johnmknight/Console10/stl/nasa switch  guards/108963-space-shuttle-toggle-switch-guard-1ca99f90-c89b-49a0-a293-3f26a061288c.pdf

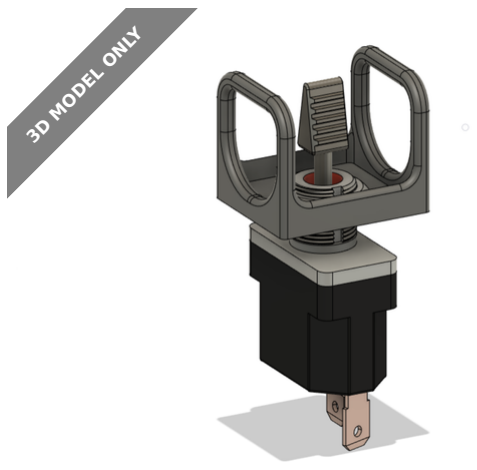
[picture p2: figure]
3D MODEL ONLY

## Summary

An accurate model of a standard space shuttle toggle switch guard, with

switch head.

Hobby & Makers (https://www.printables.com/model?categoryId=48) | > | Mechanical Parts (https://www.printables.com/model?categoryId=51)
Tags: spacex | space | rocket | switch | engineering | controller
spaceship | scifi | nasa | resin | resinprinter | toggleswitch
toggle | controlpanel | shuttle | spaceshuttle

This is an accurate recreation of a toggle switch guard used on the many

control panels in the space shuttle.

Included is a PDF are the part dimensions in case the standard thread

dimensions of the switch are different from what you choose to you use for

your project, and want to remodel it. I have also included two variations of

the switch head, one with hole and one without.

I recommend using a resin printer for the best results, and for added

realism making a cold cast copy for realistic metal weight and texture.

I have yet to find a good model of toggle switch that can be modified so

that the head can be put on, and not rotate in place without heavy switch

modification or damage. If anyone can find one please share!

I (https://www.printables.com/social/198340/about) ImAThingsGuy (https://www.printables.com/social/198340/about)

## Space Shuttle

## Toggle Switch

## Guard

VIEW IN BROWSER (https://www.printables.com/model/108963-space-shuttle-toggle-switch-guard)

updated 30. 12. 2021 | published 30. 12. 2021

## Model files

## Other files

Also please share any remixes of this or any projects you use this design

on. I have wanted to make a space shuttle/apollo cockpit styled control

panel for many years now but have never gotten around to it, I would love

to see anyone else's attempt at it or something similar.

Fun Fact; The real toggle switch guards were made of titanium to prevent

sparks in the capsule, among other reasons I'm sure.

## License

This work is licensed under a

Creative Commons (International License)

Public Domain (https://creativecommons.org/share-your-work/public-domain/cc0/)

space-shuttle-switch-head-with-hole.stl

space-shuttle-switch-head.stl

space-shuttle-switch-guard.stl

suttle-switch-final-drawing-v1.pdf

✔ | Sharing without ATTRIBUTION
✔ | Remix Culture allowed
✔ | Commercial Use
✔ | Free Cultural Works
✔ | Meets Open Definition
