johnmknight/Console10/branding/console10_social_preview.png

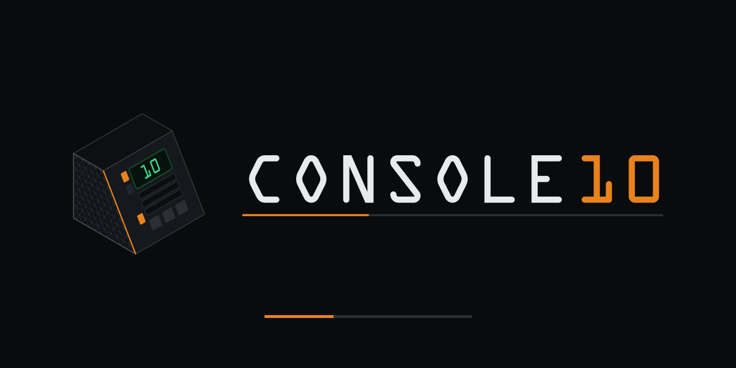
branding/console10_social_preview.png
