johnmknight/Console10/marketing/overlays/overlay_4u_front.png

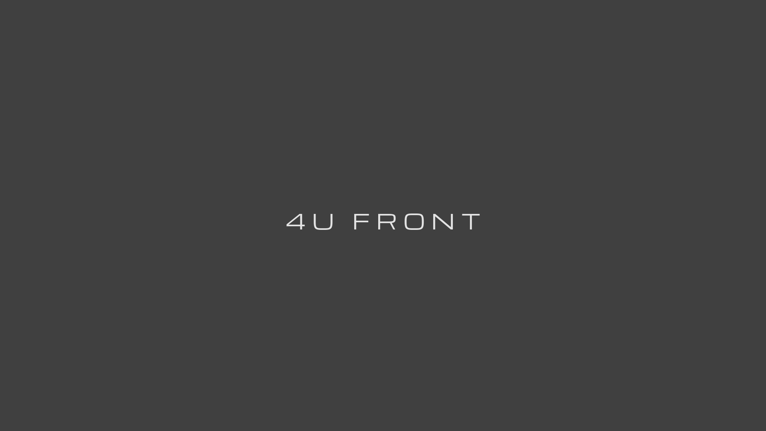
marketing/overlays/overlay_4u_front.png
