johnmknight/Console10/marketing/overlays/overlay_endcard.png

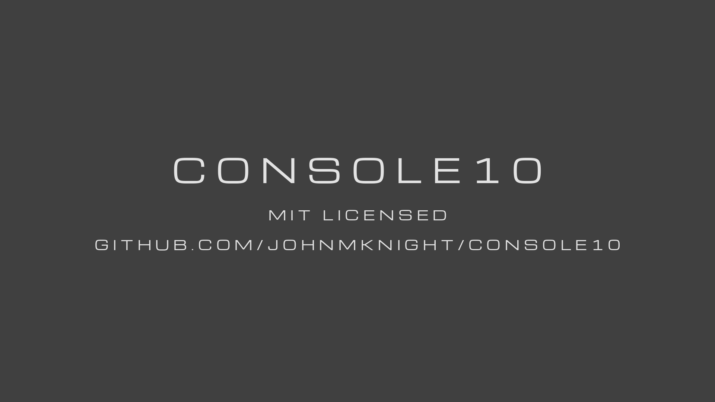
marketing/overlays/overlay_endcard.png
