johnmknight/Console10/marketing/overlays/overlay_partcount.png

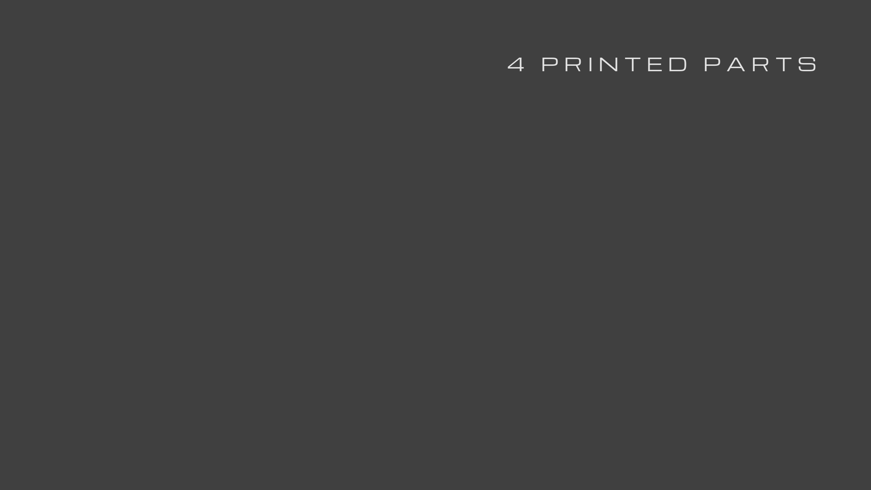
marketing/overlays/overlay_partcount.png
