johnmknight/Console10/preview/asm_macropad_iso.png

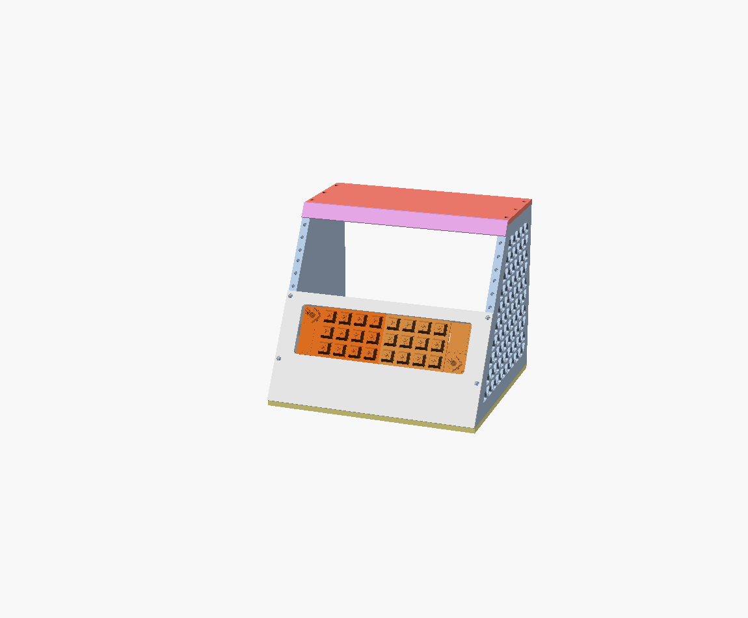
preview/asm_macropad_iso.png
