johnmknight/Console10/preview/asm_macropad_side.png

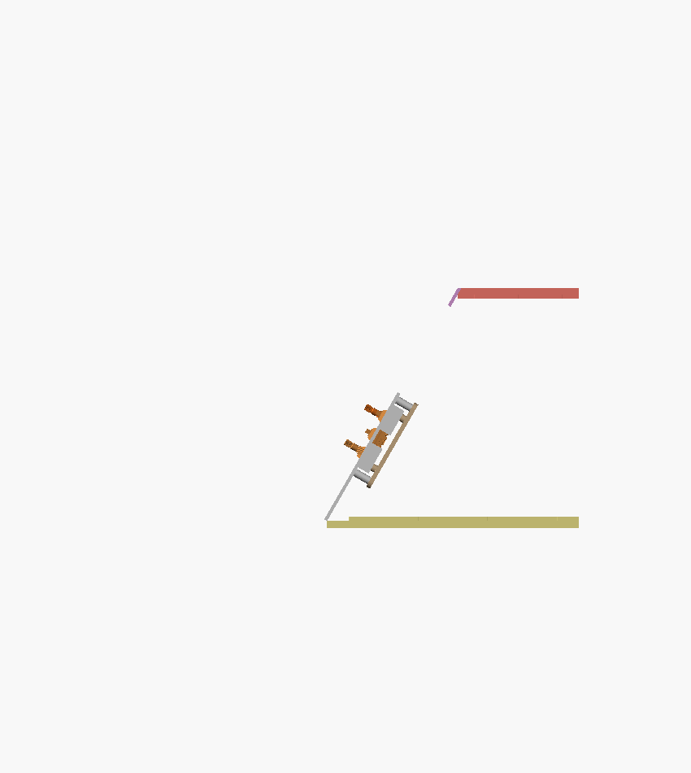
preview/asm_macropad_side.png
