johnmknight/Console10/preview/cheek_perimeter_iso.png

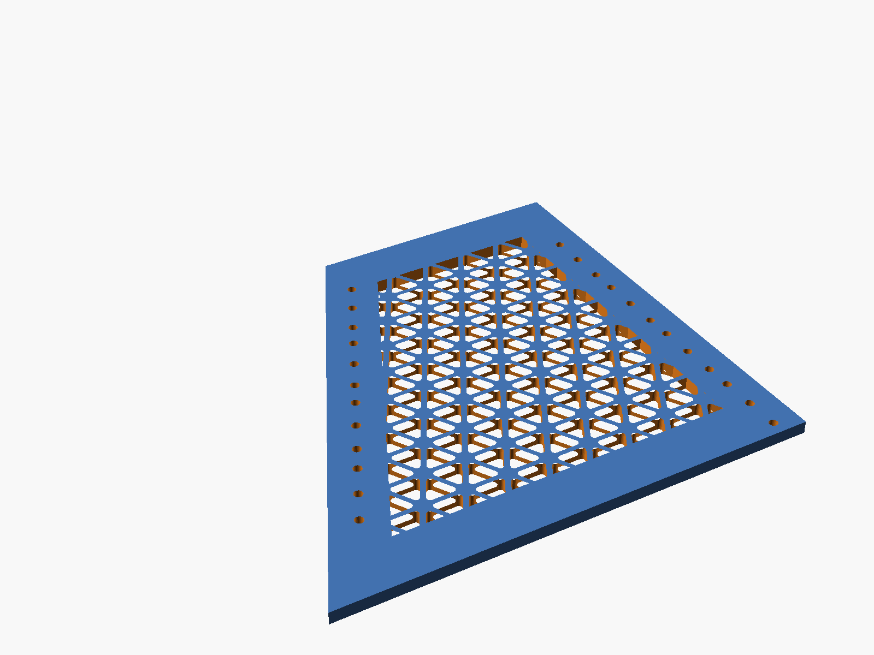
preview/cheek_perimeter_iso.png
