johnmknight/Console10/preview/cheek_perimeter_top.png

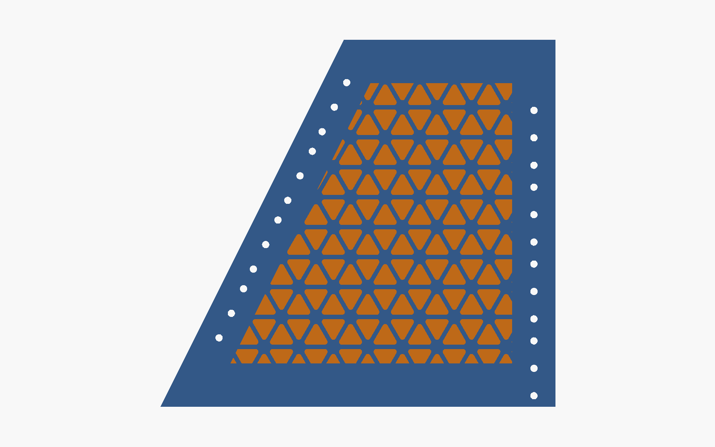
preview/cheek_perimeter_top.png
