johnmknight/Console10/preview/dsky_front.png

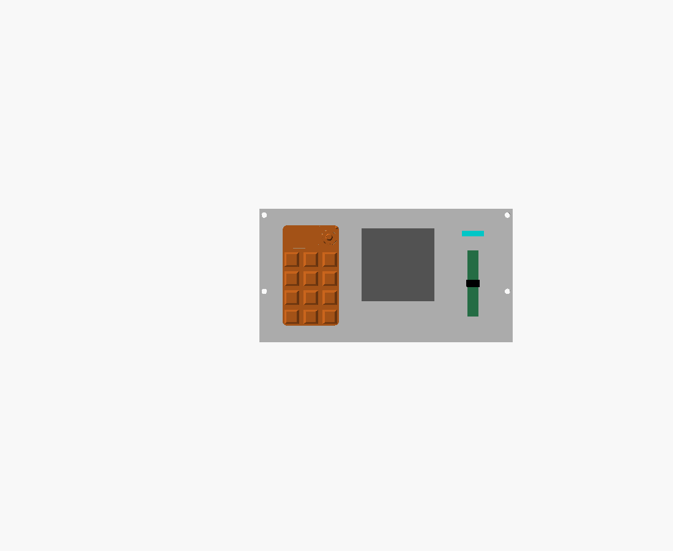
preview/dsky_front.png
