johnmknight/Console10/preview/dsky_iso.png

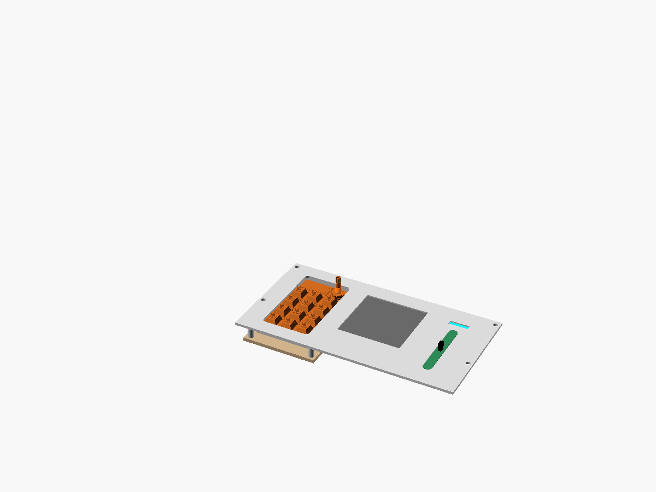
preview/dsky_iso.png
