johnmknight/Console10/preview/dsky_rear.png

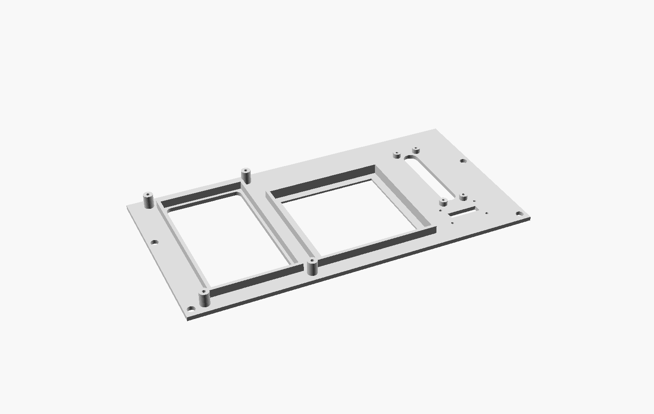
preview/dsky_rear.png
