johnmknight/Console10/preview/guard_A_front.png

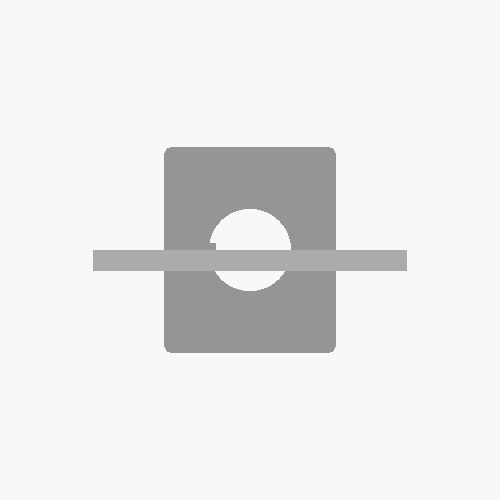
preview/guard_A_front.png
