johnmknight/Console10/preview/guard_A_top.png

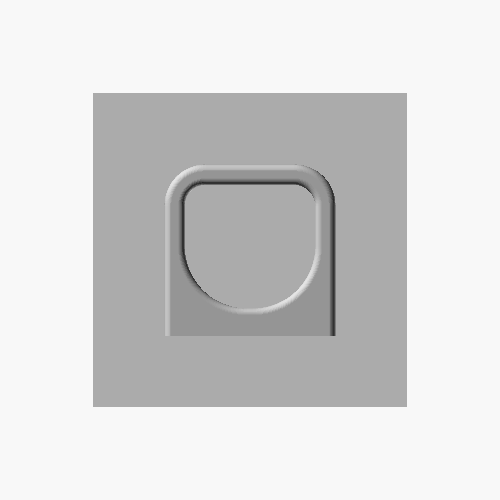
preview/guard_A_top.png
