johnmknight/Console10/preview/guard_front.png

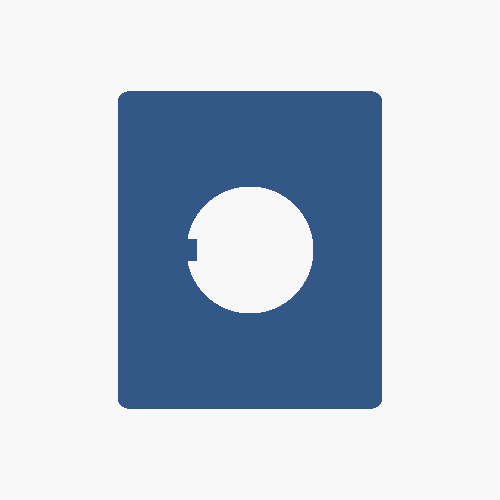
preview/guard_front.png
