johnmknight/Console10/preview/guard_side.png

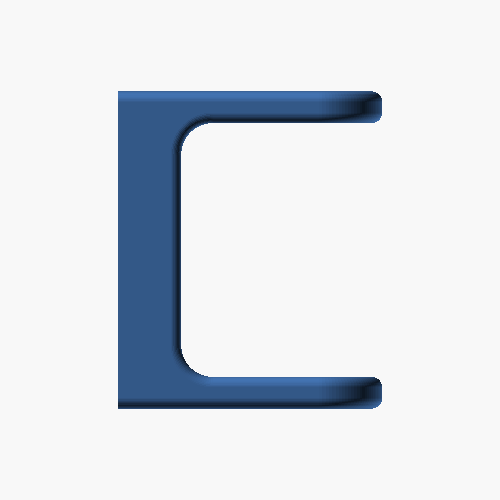
preview/guard_side.png
