johnmknight/Console10/preview/guard_stand_A.png

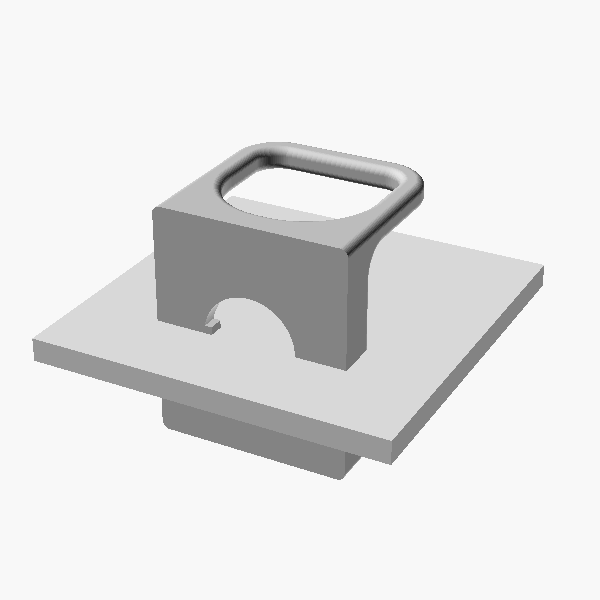
preview/guard_stand_A.png
