johnmknight/Console10/preview/guard_top.png

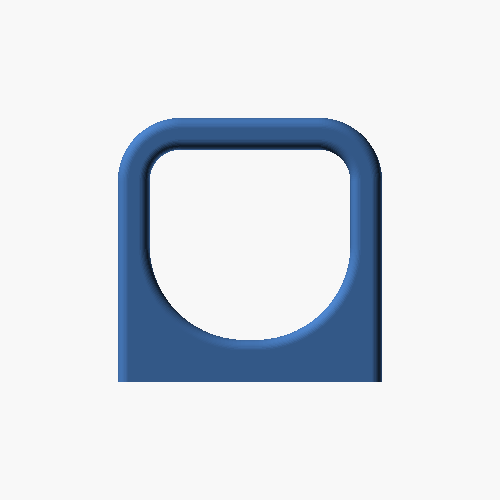
preview/guard_top.png
