johnmknight/Console10/preview/hp_backplate.png

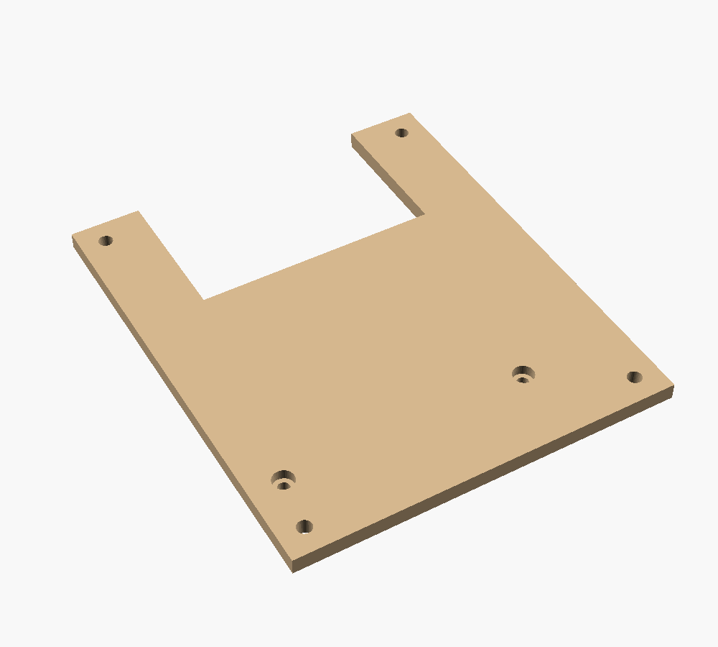
preview/hp_backplate.png
