johnmknight/Console10/preview/hp_sq_front.png

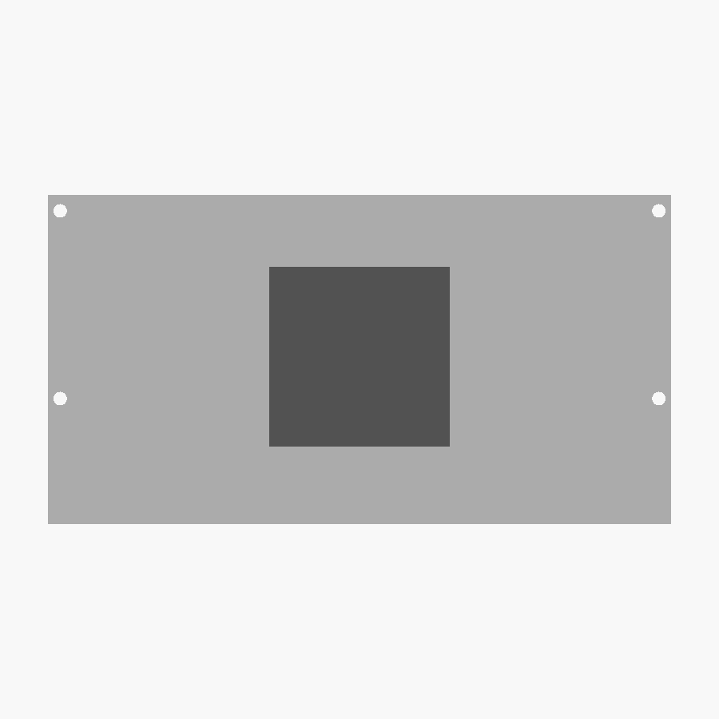
preview/hp_sq_front.png
