johnmknight/Console10/preview/hp_sq_iso.png

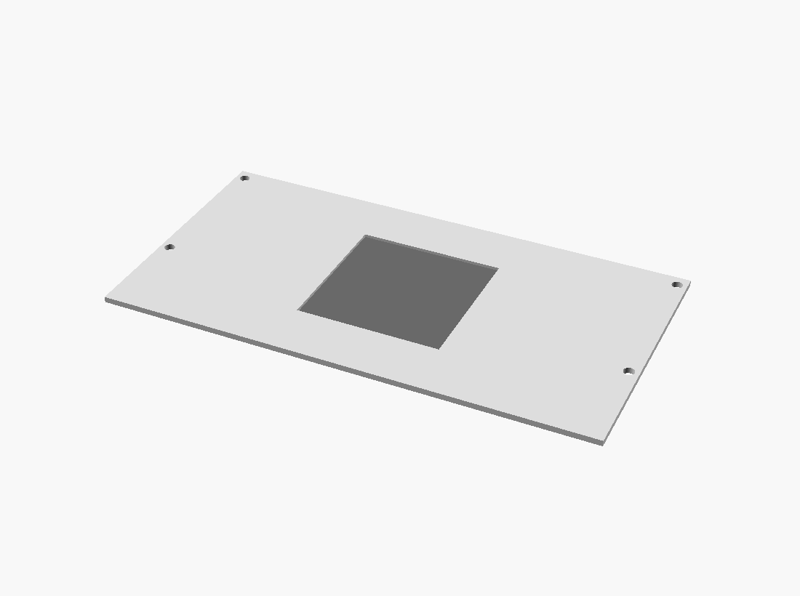
preview/hp_sq_iso.png
