johnmknight/Console10/preview/mp_pair_front.png

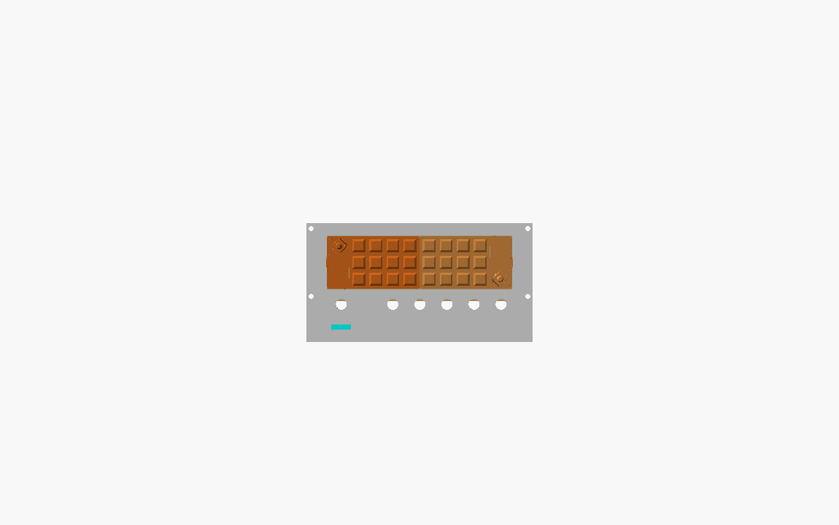
preview/mp_pair_front.png
