johnmknight/Console10/preview/oled_closeup.png

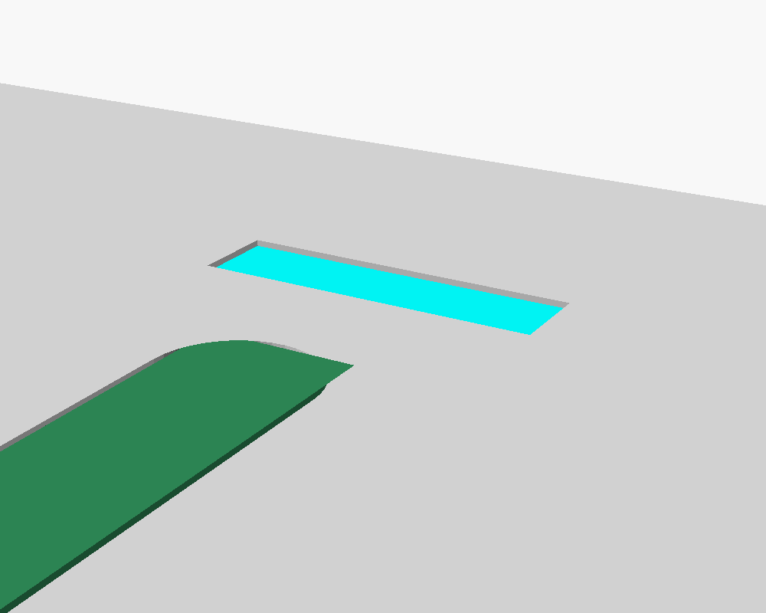
preview/oled_closeup.png
