johnmknight/Console10/preview/ref_bracket_top.png

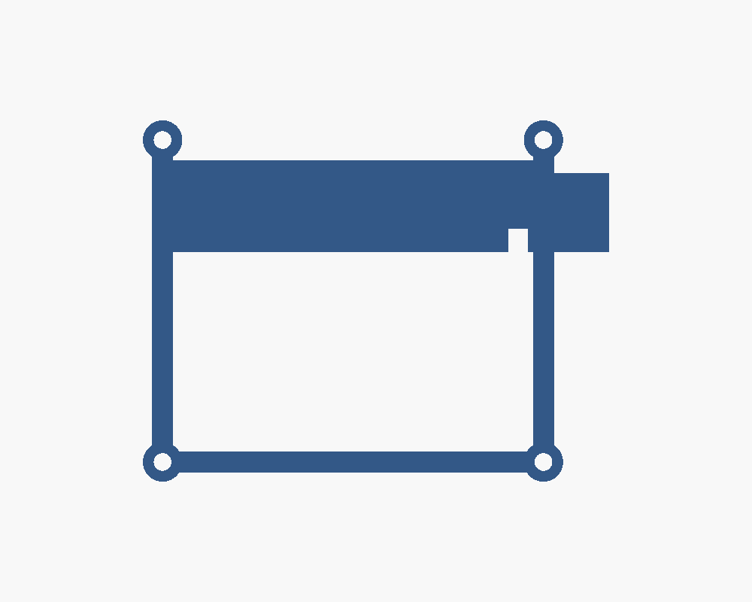
preview/ref_bracket_top.png
