johnmknight/Console10/preview/ref_wallback_bot.png

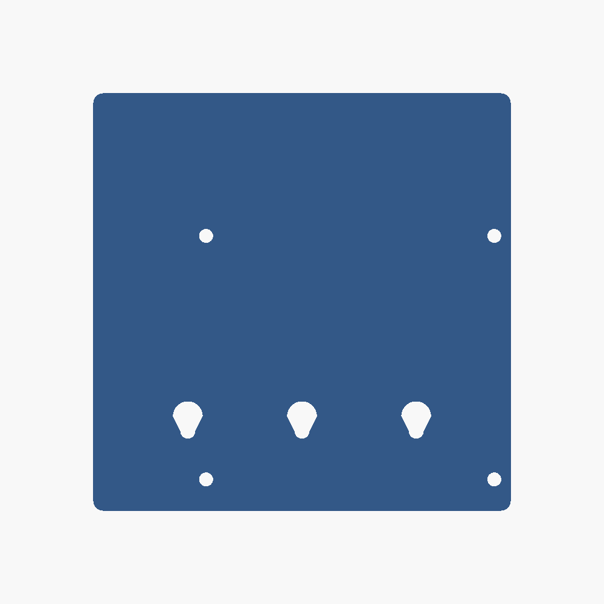
preview/ref_wallback_bot.png
