johnmknight/Console10/preview/ref_wallback_iso.png

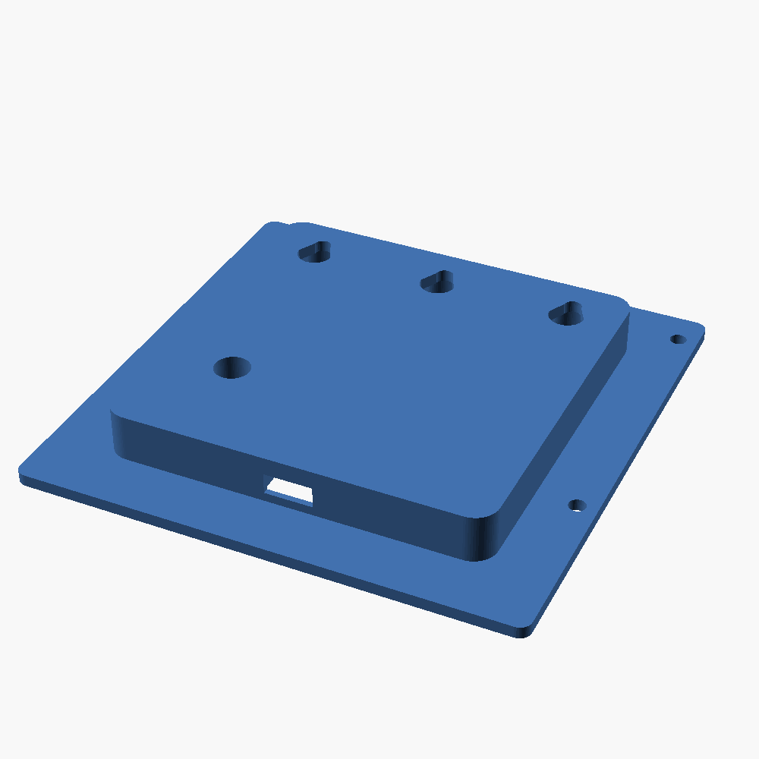
preview/ref_wallback_iso.png
