johnmknight/Console10/preview/ref_wallback_top.png

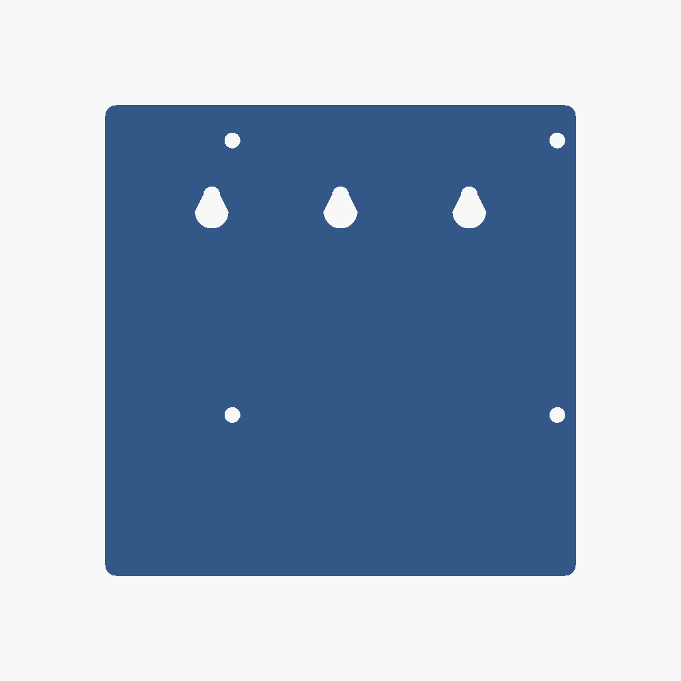
preview/ref_wallback_top.png
