johnmknight/Console10/preview/screen_slider_front.png

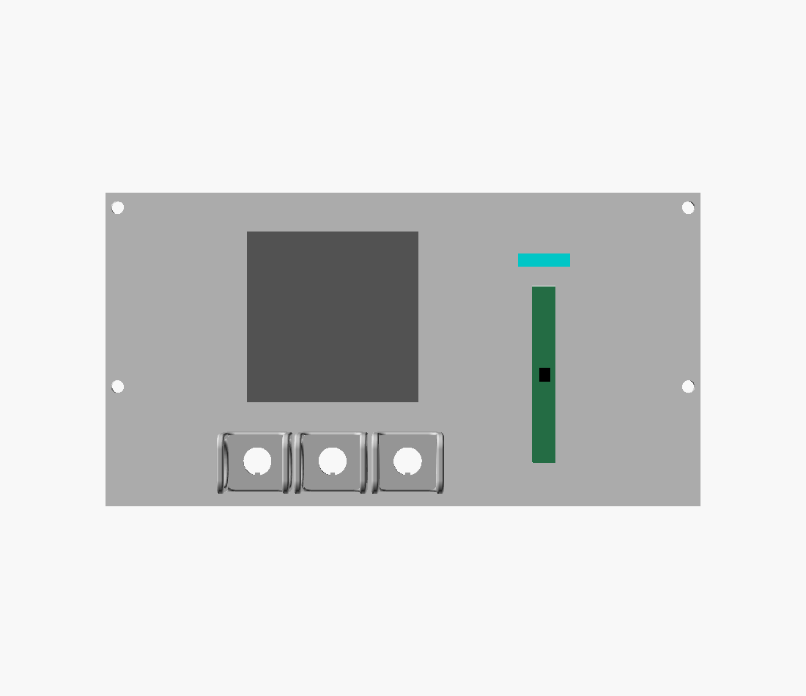
preview/screen_slider_front.png
