johnmknight/Console10/preview/screen_slider_iso.png

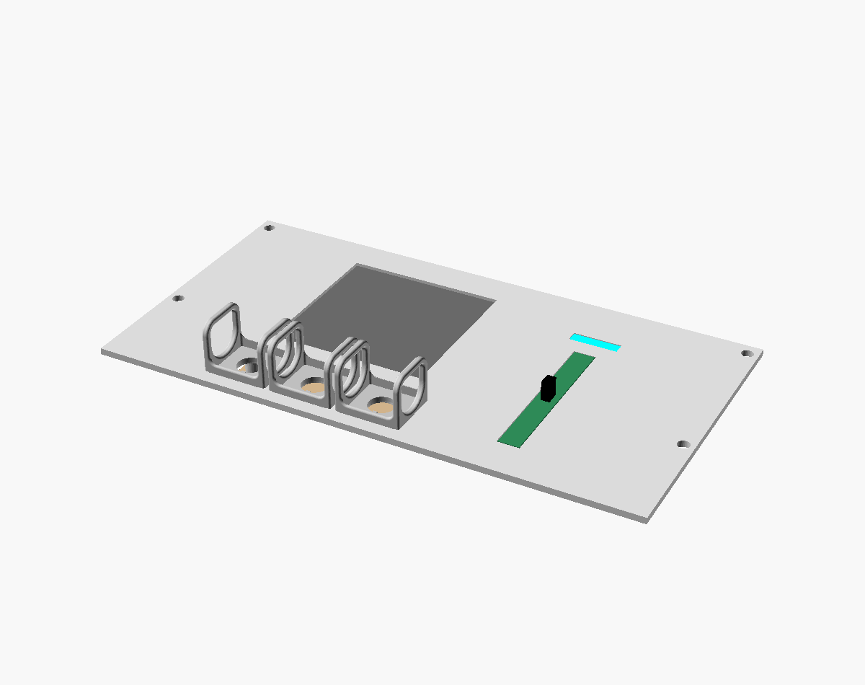
preview/screen_slider_iso.png
