johnmknight/Console10/preview/screen_slider_rear.png

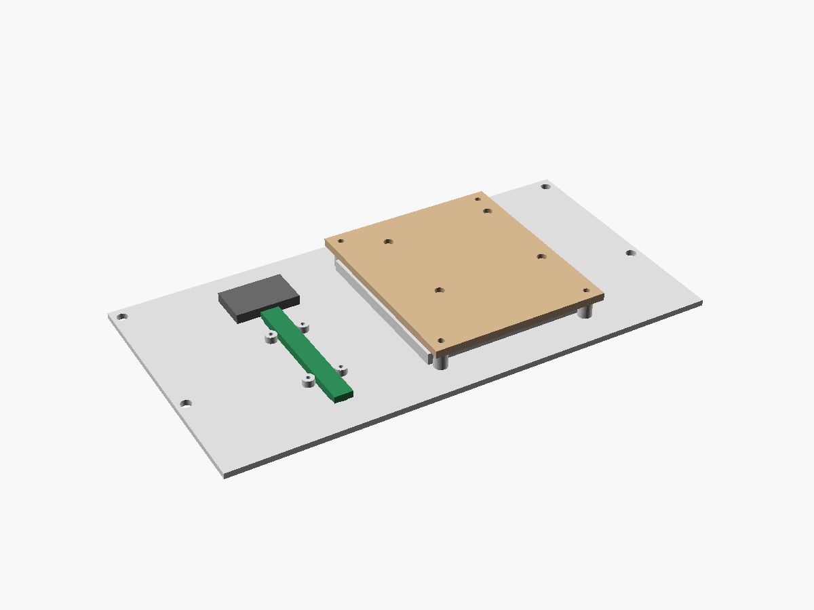
preview/screen_slider_rear.png
