johnmknight/Console10/preview/screen_slider_sec.png

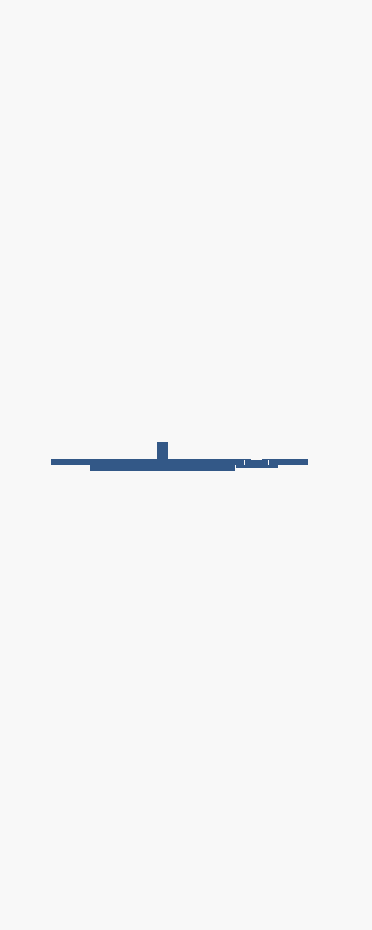
preview/screen_slider_sec.png
