johnmknight/Console10/preview/slider_closeup.png

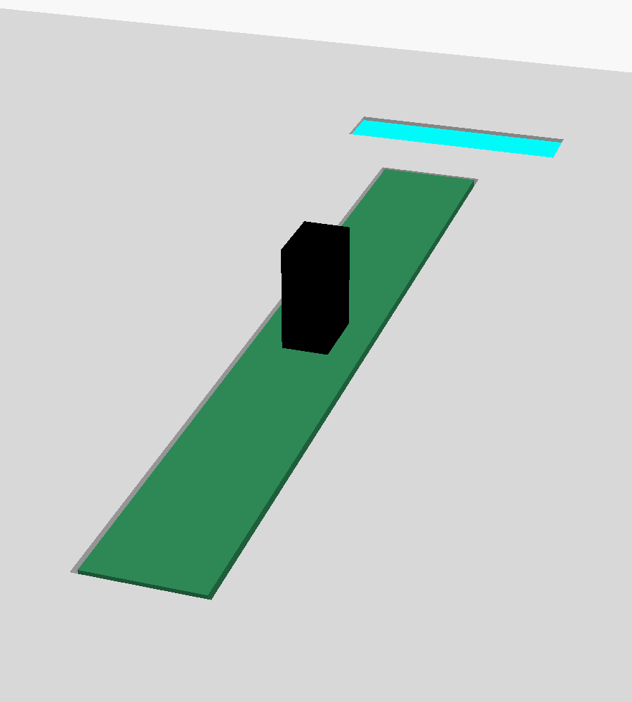
preview/slider_closeup.png
