johnmknight/Console10/stl/Console10_phone_2u_lever.stl

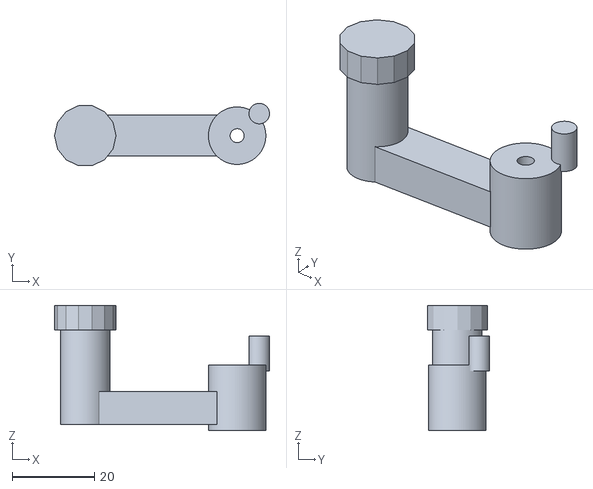
[picture p51: CAD file, 2026-08-08]
stl/Console10_phone_2u_lever.stl
52.4 x 15.2 x 30.5
