johnmknight/Console10/Console10_isogrid-new.stl

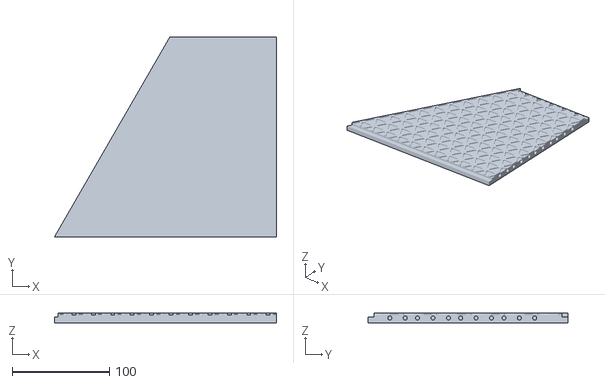
[picture p52: CAD file, 2026-07-28]
Console10_isogrid-new.stl
228.6 x 205.5 x 10.0
