johnmknight/Console10/preview/hp_sq.stl

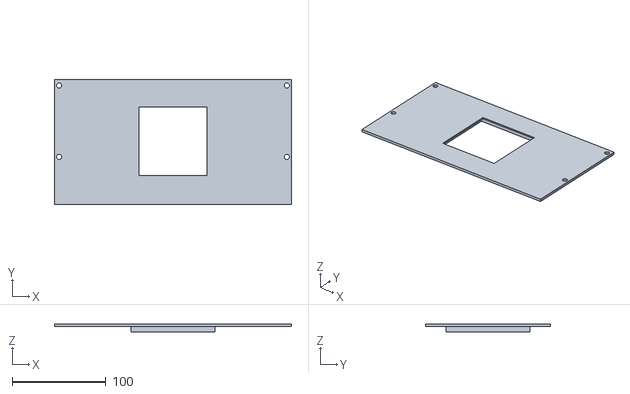
[picture p53: CAD file, 2026-07-28]
preview/hp_sq.stl
253.0 x 133.3 x 9.00
