johnmknight/Console10/stl/Console10_phone_2u_ejector.stl

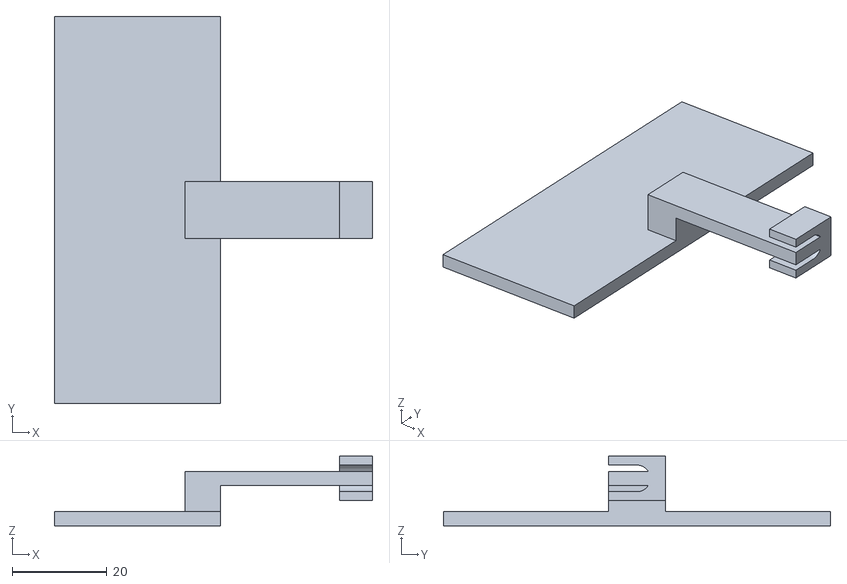
[picture p54: CAD file, 2026-08-08]
stl/Console10_phone_2u_ejector.stl
67.0 x 81.6 x 14.7
