johnmknight/Console10/Console10_guard_bank3.stl

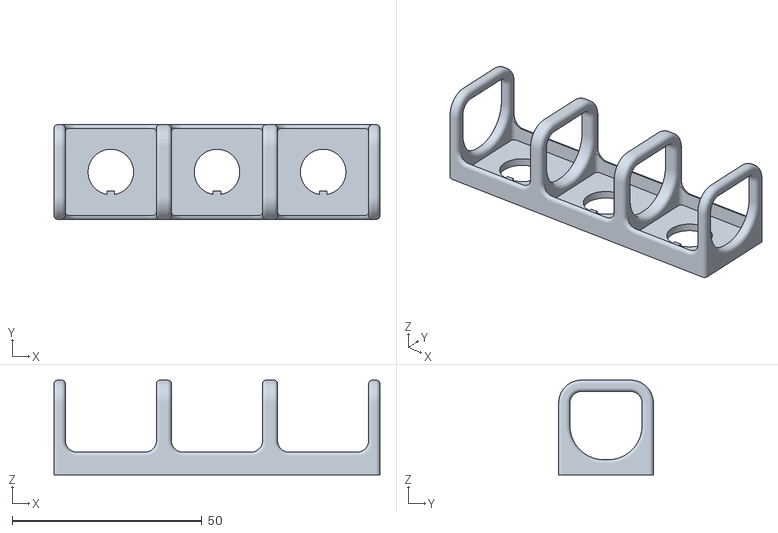
[picture p55: CAD file, 2026-06-17]
Console10_guard_bank3.stl
86.0 x 25.0 x 25.0
