johnmknight/Console10/preview/dsky_hp_backplate.stl

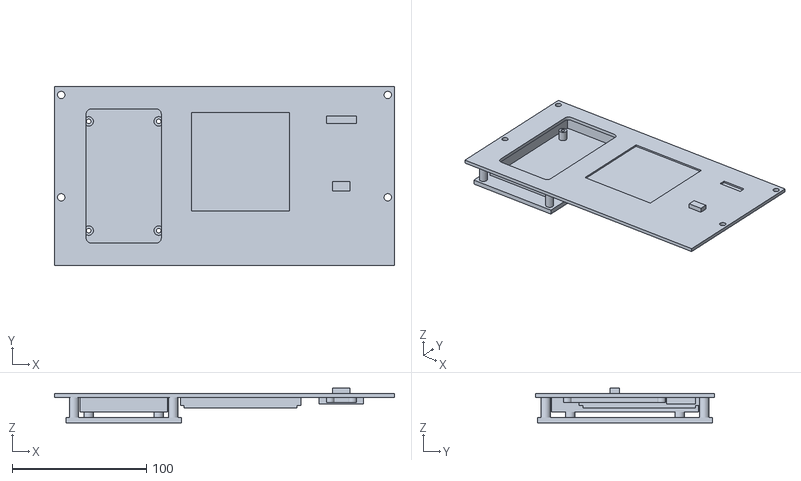
[picture p56: CAD file, 2026-07-28]
preview/dsky_hp_backplate.stl
253.0 x 133.3 x 26.0
