johnmknight/Console10/stl/Console10_top.stl

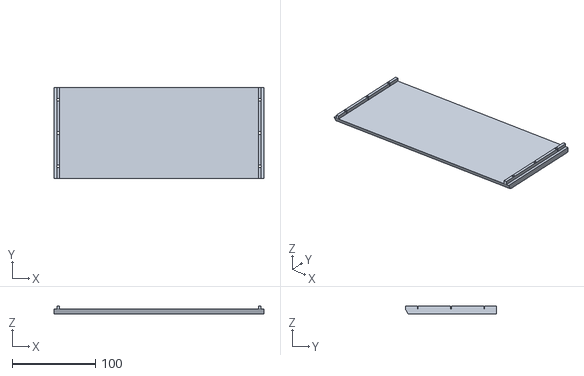
[picture p57: CAD file, 2026-05-28]
stl/Console10_top.stl
253.0 x 110.0 x 10.0
