johnmknight/Console10/Console10_macropad_mount_board.stl

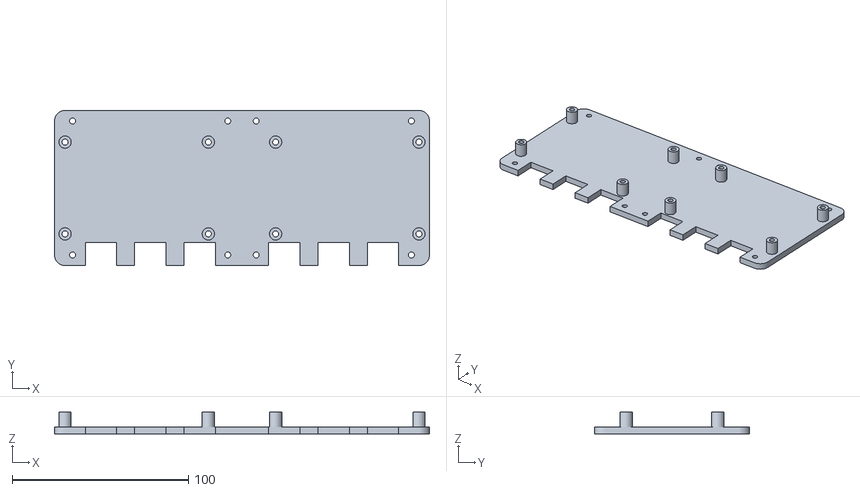
[picture p58: CAD file, 2026-06-17]
Console10_macropad_mount_board.stl
212.7 x 88.0 x 12.4
