johnmknight/Console10/preview/dsky_mp_backplate.stl

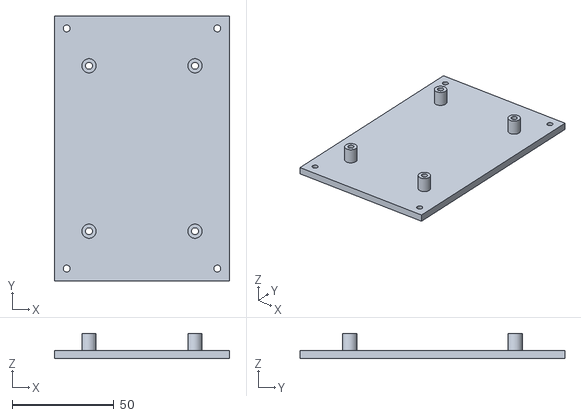
[picture p59: CAD file, 2026-07-28]
preview/dsky_mp_backplate.stl
86.0 x 130.0 x 12.4
