johnmknight/Console10/Console10_macropad_pair_panel.stl

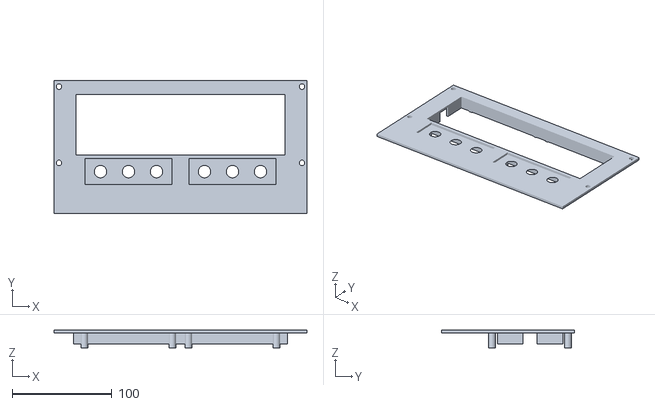
[picture p60: CAD file, 2026-06-17]
Console10_macropad_pair_panel.stl
253.0 x 133.3 x 18.0
