johnmknight/Console10/stl/Console10_bottom.stl

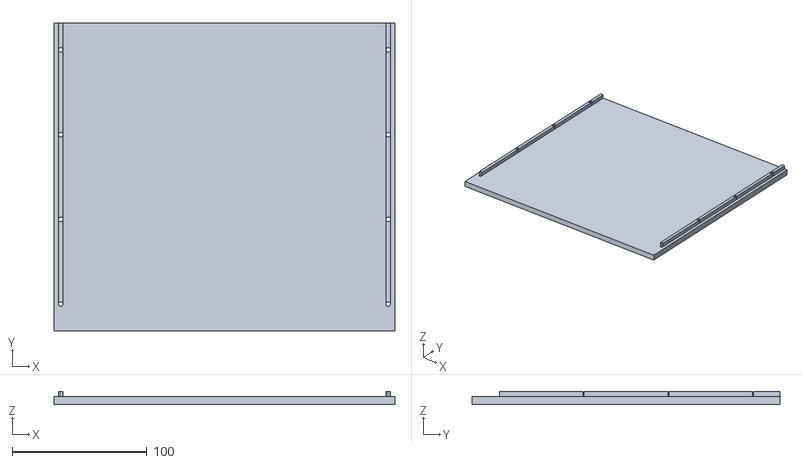
[picture p61: CAD file, 2026-05-28]
stl/Console10_bottom.stl
253.0 x 228.6 x 10.0
