johnmknight/Console10/Console10_macropad_pair_faceplate.stl

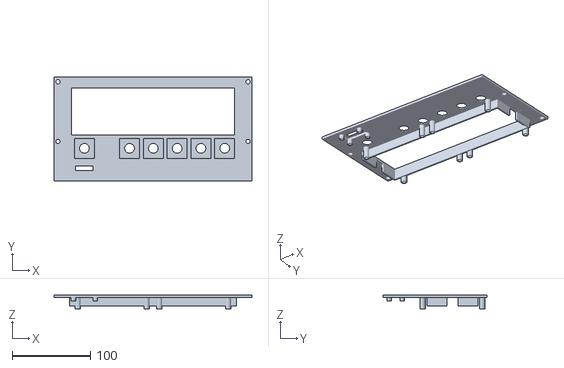
[picture p62: CAD file, 2026-06-14]
Console10_macropad_pair_faceplate.stl
253.0 x 133.3 x 18.0
