johnmknight/Console10/stl/Console10_front_insert.stl

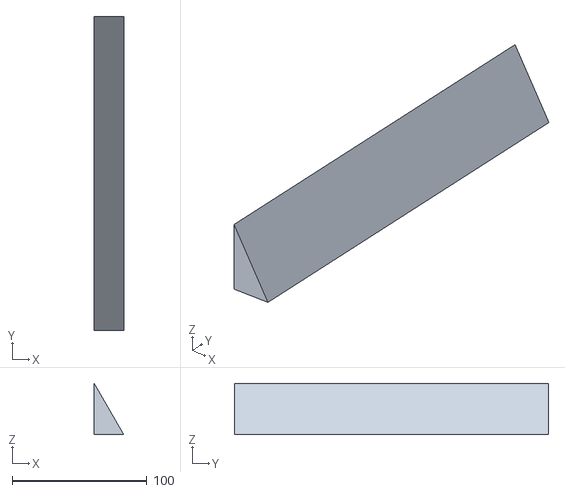
[picture p63: CAD file, 2026-05-28]
stl/Console10_front_insert.stl
21.9 x 232.6 x 38.0
