johnmknight/Console10/Console10_sd_holder_handled.stl

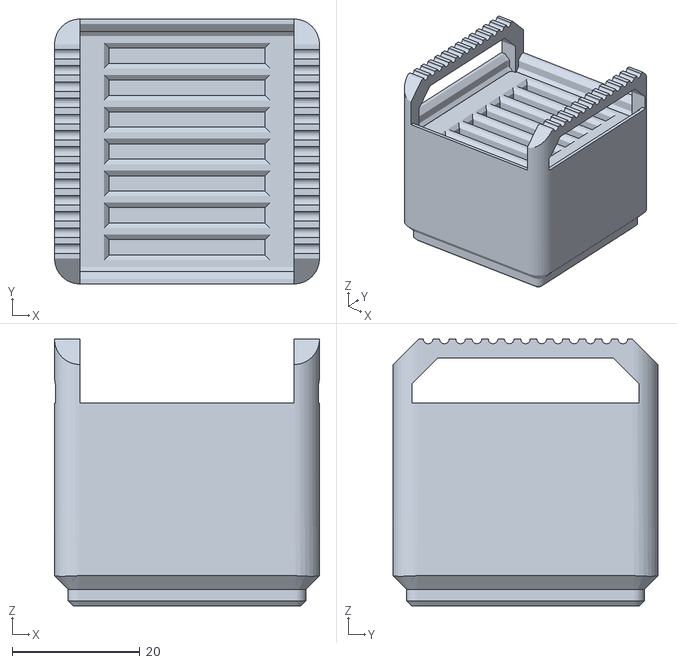
[picture p64: CAD file, 2026-06-14]
Console10_sd_holder_handled.stl
41.5 x 41.5 x 41.8
