johnmknight/Console10/Console10_screen_slider_panel.stl

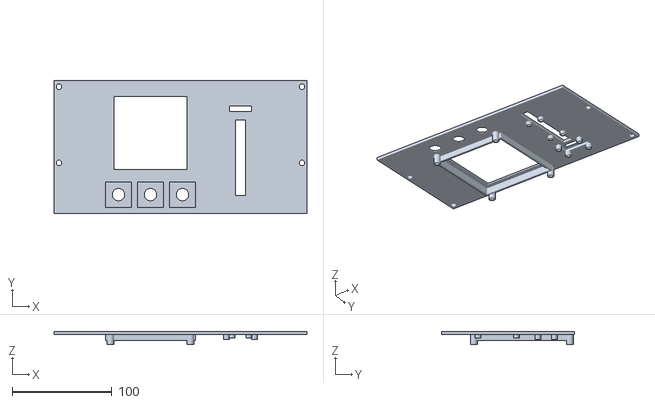
[picture p65: CAD file, 2026-06-14]
Console10_screen_slider_panel.stl
253.0 x 133.3 x 13.0
