johnmknight/Console10/Console10_screen_slider_hp_backplate.stl

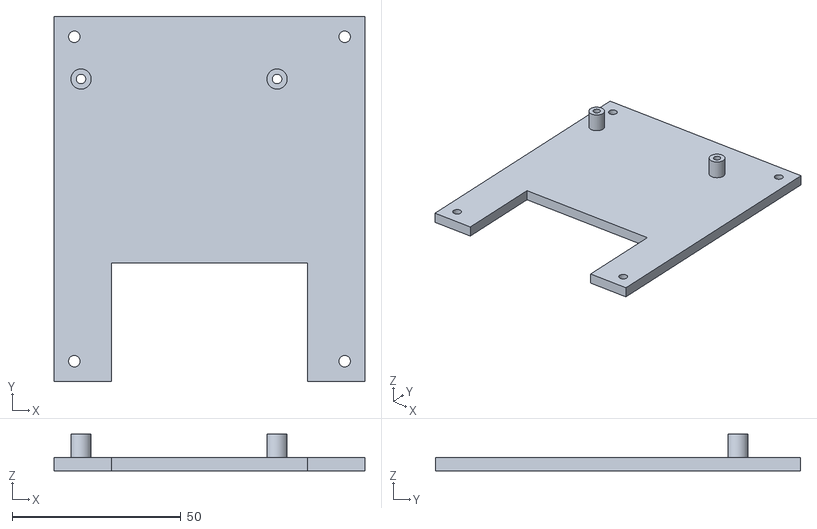
[picture p66: CAD file, 2026-06-14]
Console10_screen_slider_hp_backplate.stl
92.0 x 108.0 x 10.9
