johnmknight/Console10/Console10_macropad_pair_backplate.stl

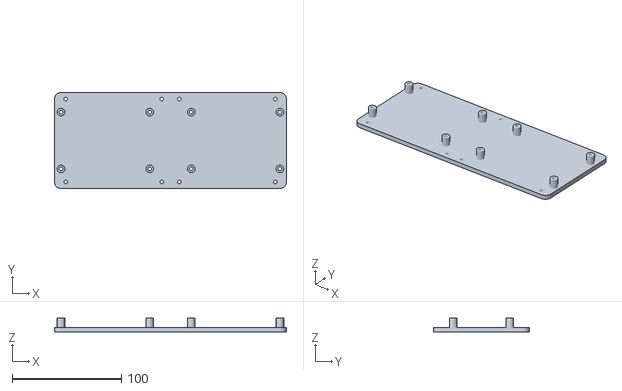
[picture p67: CAD file, 2026-06-14]
Console10_macropad_pair_backplate.stl
212.7 x 88.0 x 12.4
