johnmknight/Console10/Console10_bit_holder_handled.stl

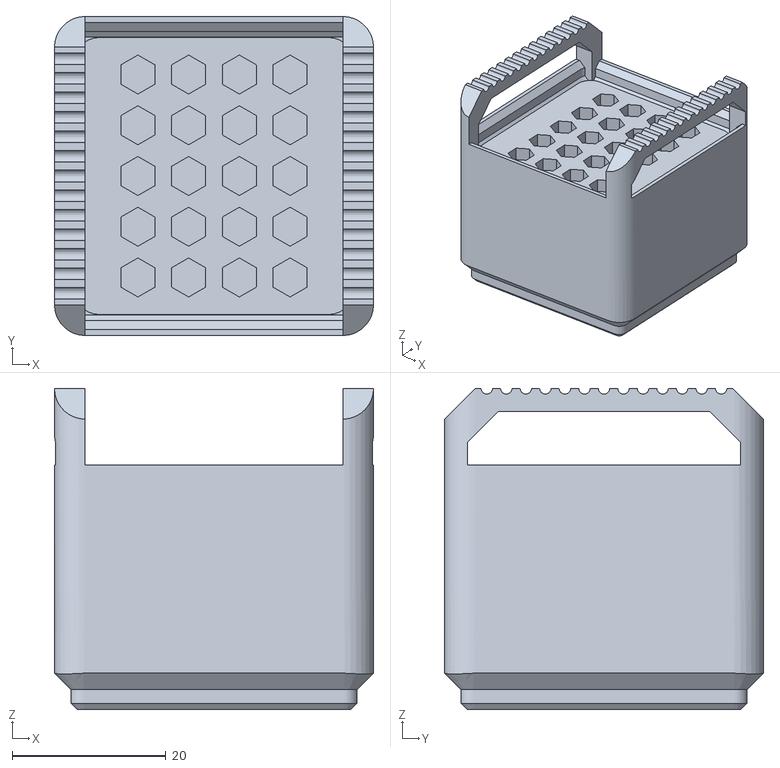
[picture p68: CAD file, 2026-06-11]
Console10_bit_holder_handled.stl
41.5 x 41.5 x 41.8
