johnmknight/Console10/Console10_slant_cap_tall.stl

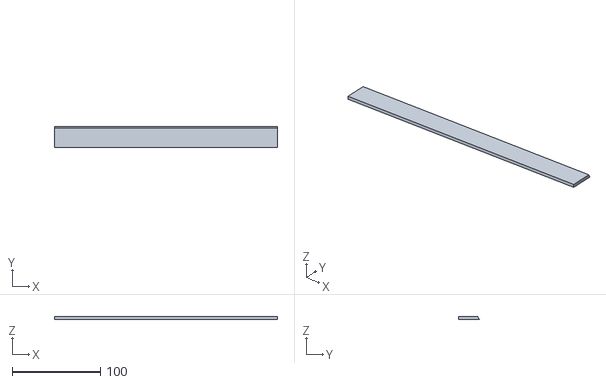
[picture p69: CAD file, 2026-06-06]
Console10_slant_cap_tall.stl
253.0 x 23.4 x 3.00
