johnmknight/Console10/Console10_slant_cap.stl

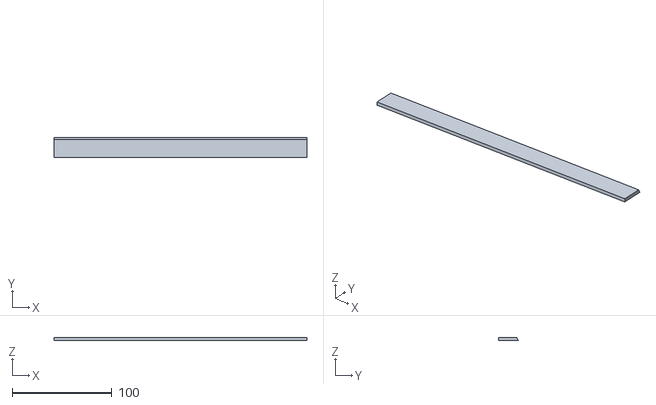
[picture p70: CAD file, 2026-06-06]
Console10_slant_cap.stl
253.0 x 19.9 x 3.00
