johnmknight/Console10/Console10_bluray_2u_faceplate.stl

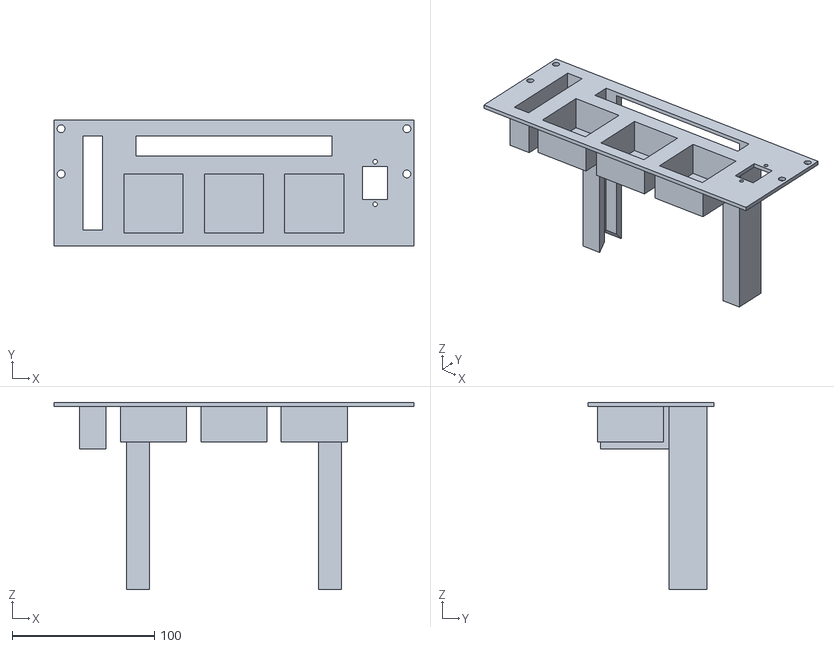
[picture p71: CAD file, 2026-06-02]
Console10_bluray_2u_faceplate.stl
253.0 x 88.9 x 131.7
