johnmknight/Console10/Console10_aux_2u_faceplate_v02.stl

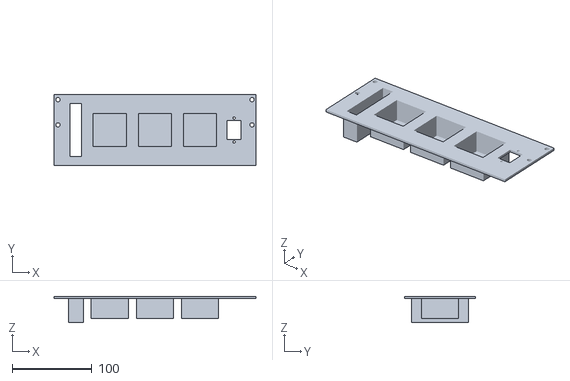
[picture p72: CAD file, 2026-05-30]
Console10_aux_2u_faceplate_v02.stl
253.0 x 88.9 x 33.0
