johnmknight/Console10/Console10_lcd_simple_faceplate_v01.stl

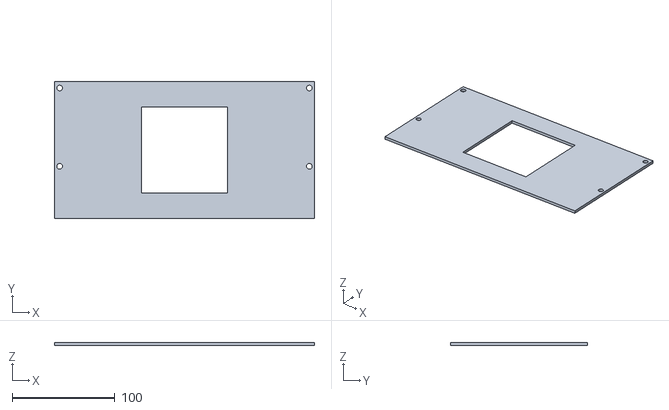
[picture p73: CAD file, 2026-05-30]
Console10_lcd_simple_faceplate_v01.stl
253.0 x 133.3 x 3.00
