johnmknight/Console10/MiniRax-plain-mini-faceplate.stl

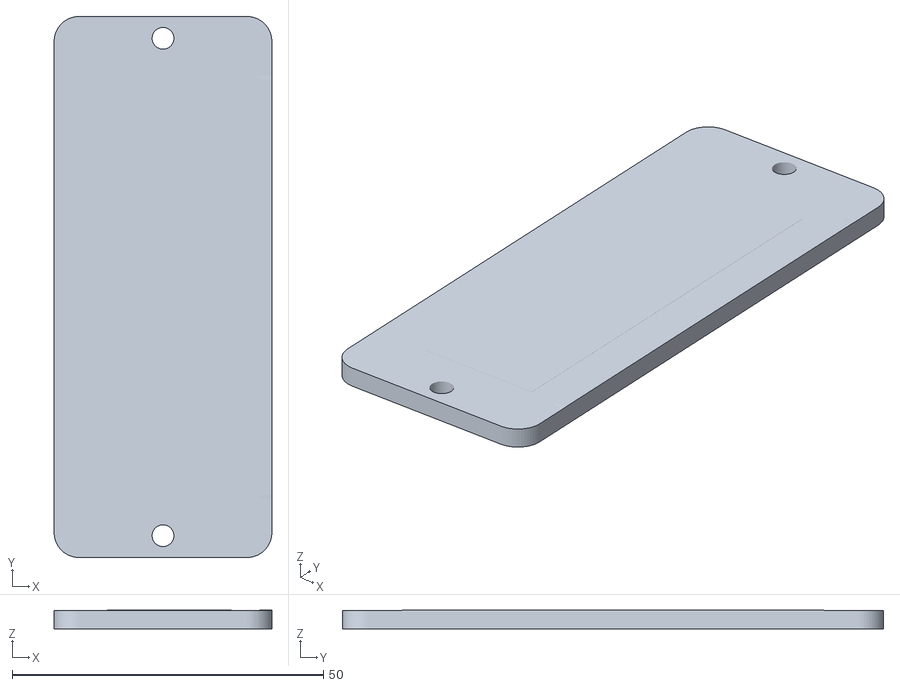
[picture p74: CAD file, 2026-05-28]
MiniRax-plain-mini-faceplate.stl
35.0 x 87.0 x 3.03
