johnmknight/Console10/NEW_NASA_TOP.stl

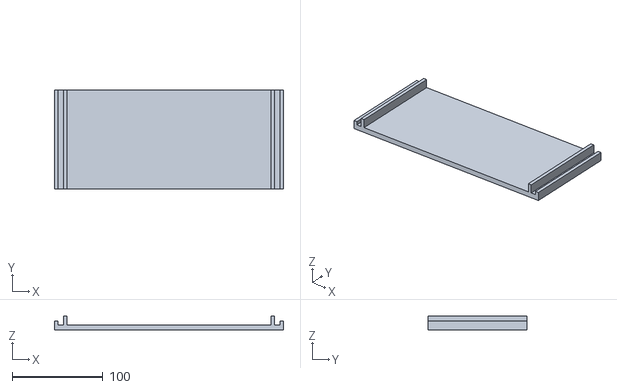
[picture p75: CAD file, 2026-05-28]
NEW_NASA_TOP.stl
253.0 x 109.9 x 16.0
