johnmknight/Console10/MiniRaxFacePlate1.stl

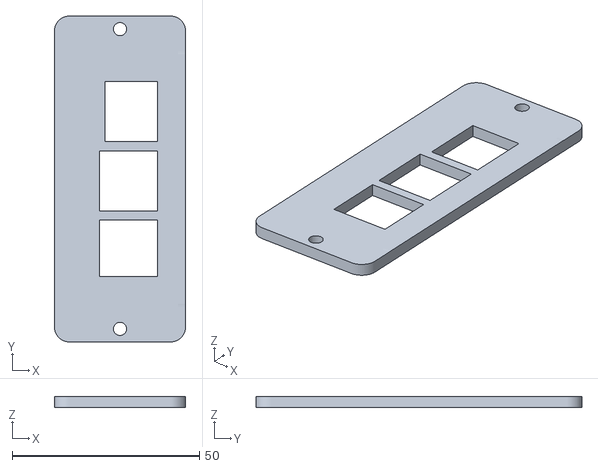
[picture p76: CAD file, 2026-05-28]
MiniRaxFacePlate1.stl
35.0 x 87.0 x 3.03
