johnmknight/Console10/NASA_Insert_Front.stl

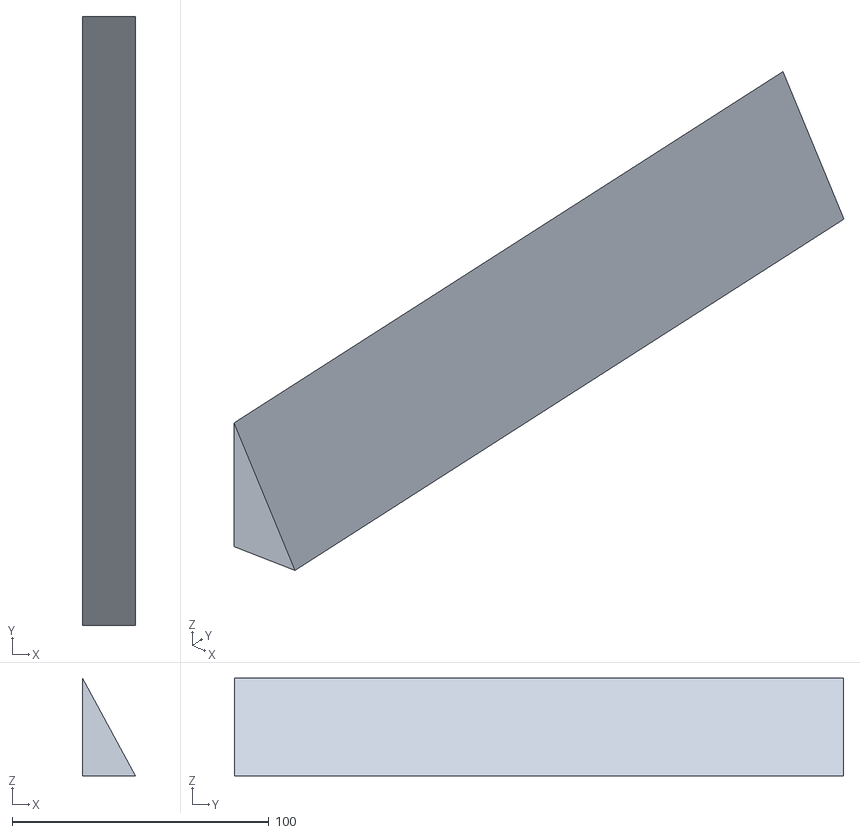
[picture p77: CAD file, 2026-05-28]
NASA_Insert_Front.stl
20.6 x 237.3 x 38.0
