johnmknight/Console10/new_nasa_bottom.stl

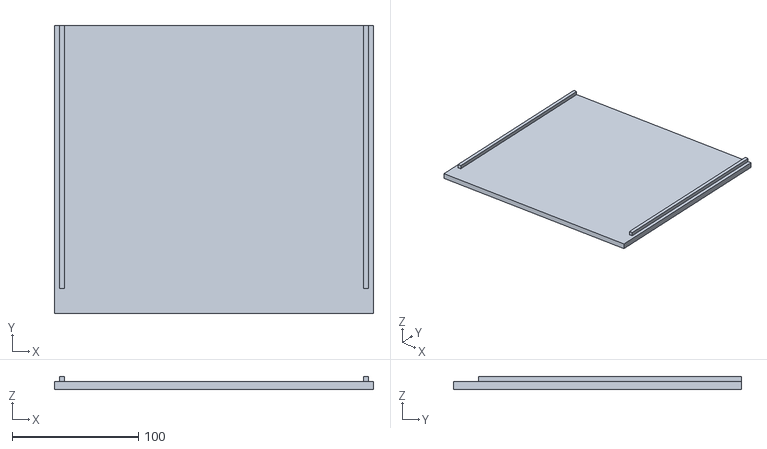
[picture p78: CAD file, 2026-05-28]
new_nasa_bottom.stl
253.0 x 228.6 x 10.0
