johnmknight/Console10/_stl_top.scad

import("C:/3d files/Gridfinity/1x1x4_sd_card_holder_7.stl", convexity=12);
