johnmknight/Console10/preview/_stlview.scad

import(F);
