johnmknight/Console10/preview/macropad_measure.png

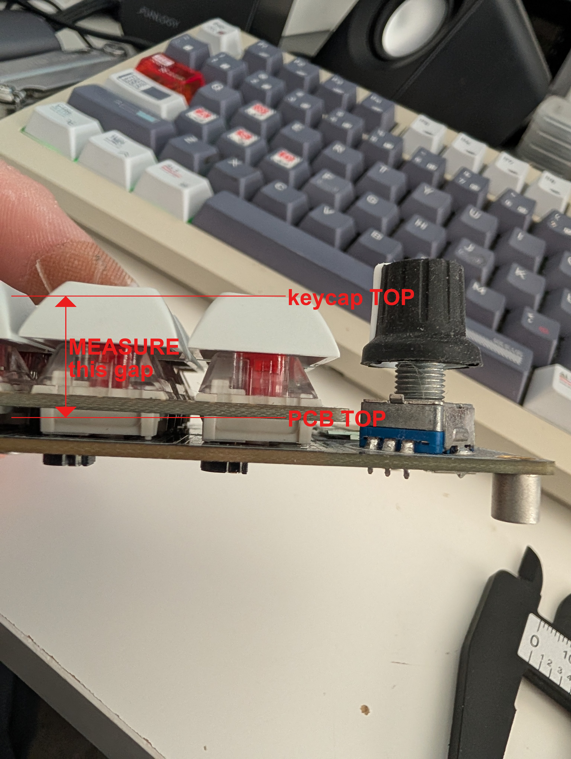
preview/macropad_measure.png
